telzo2000/cool936/first_design/cool936sbydss_micro-2.jpg

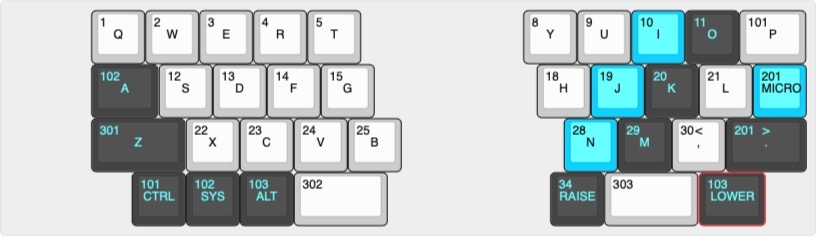
first_design/cool936sbydss_micro-2.jpg
