telzo2000/cool936/img/img00006.jpg

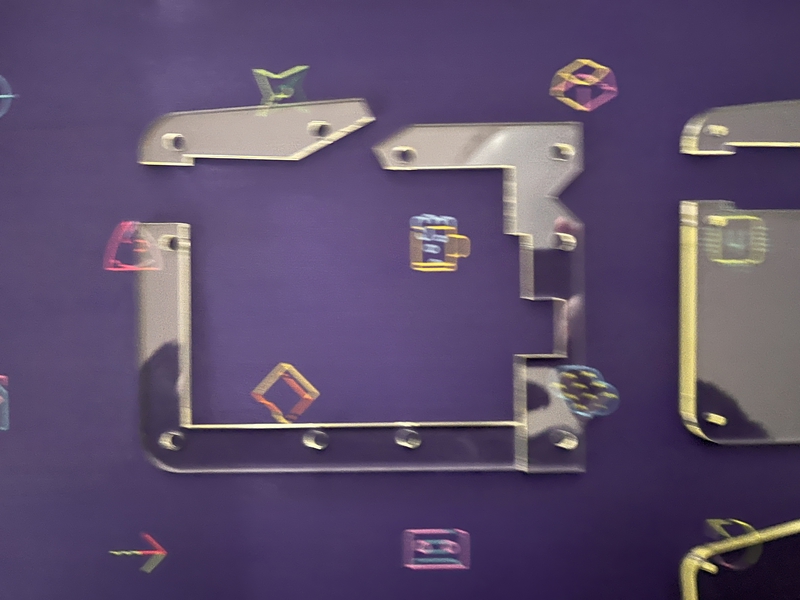
img/img00006.jpg
