telzo2000/cool936/img/img00012.jpg

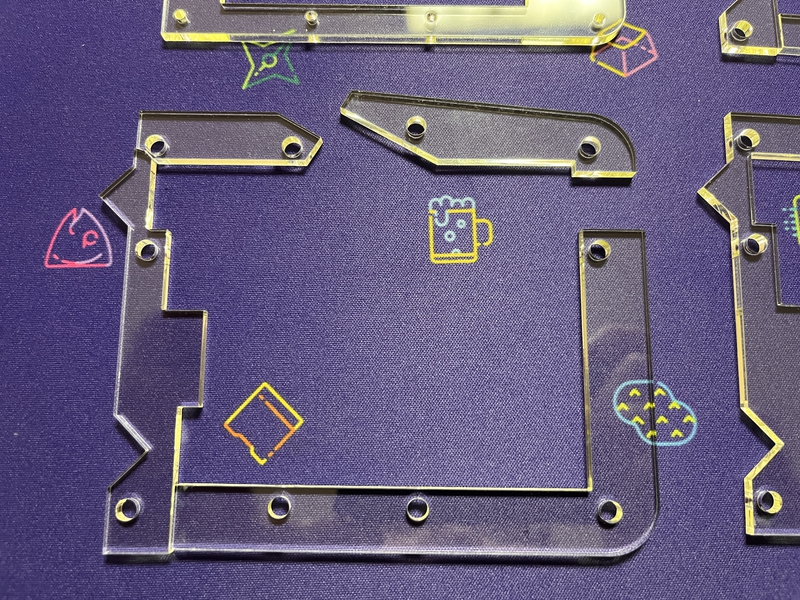
img/img00012.jpg
