telzo2000/cool936/img/img00031.jpg

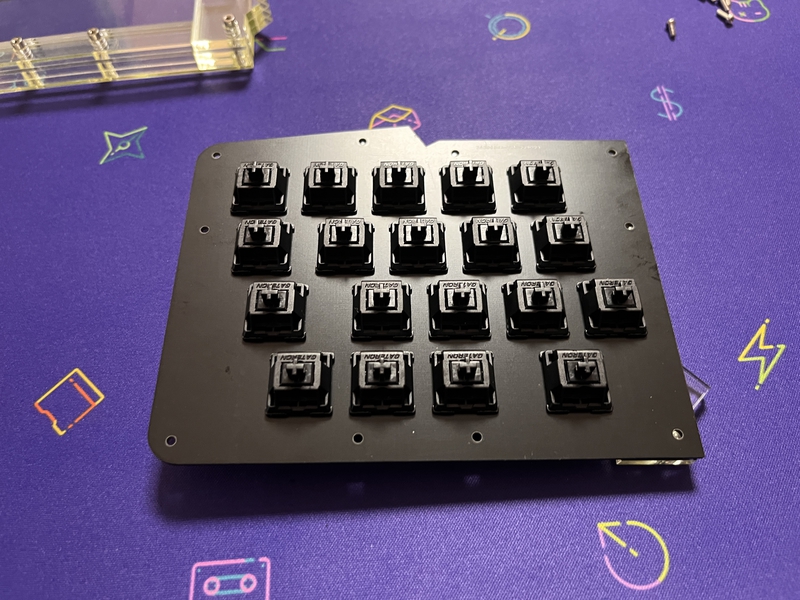
img/img00031.jpg
